benPark20/74-Orange-Opps-mini10/Mini FRC 10 CAD/Master Part Studio - Hex Spacer.step

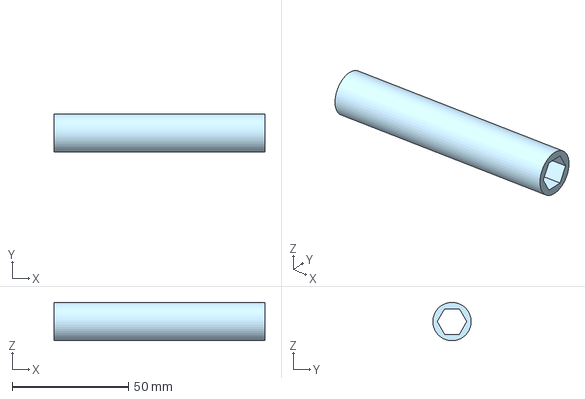
[picture p15: CAD file, 2024-07-15]
Mini FRC 10 CAD/Master Part Studio - Hex Spacer.step
90.9 x 16.5 x 16.5 mm
