benPark20/74-Orange-Opps-mini10/Mini FRC 10 CAD/Intake+drivetrain V1.stl

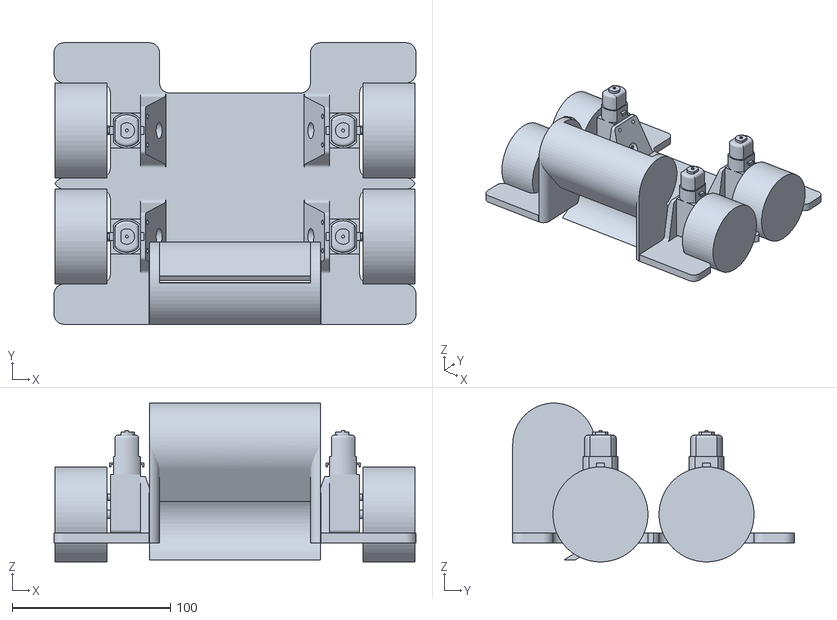
[picture p16: CAD file, 2024-07-09]
Mini FRC 10 CAD/Intake+drivetrain V1.stl
228.6 x 177.8 x 100.3
